rohid7401/MarEnMovimiento/Pruebas/Caja Front.png

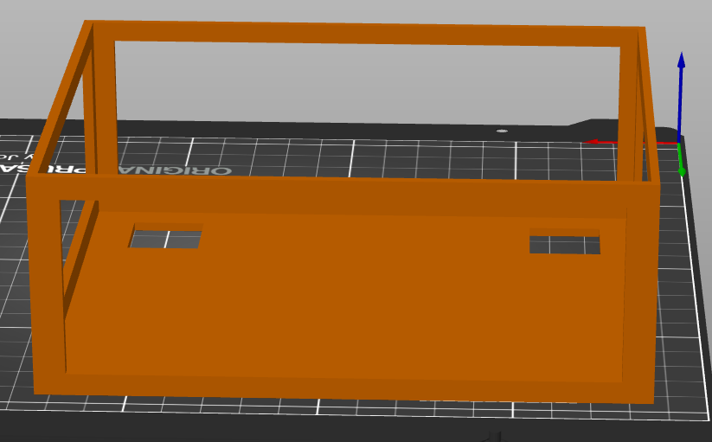
Pruebas/Caja Front.png
