rohid7401/MarEnMovimiento/Pruebas/Caja Top.png

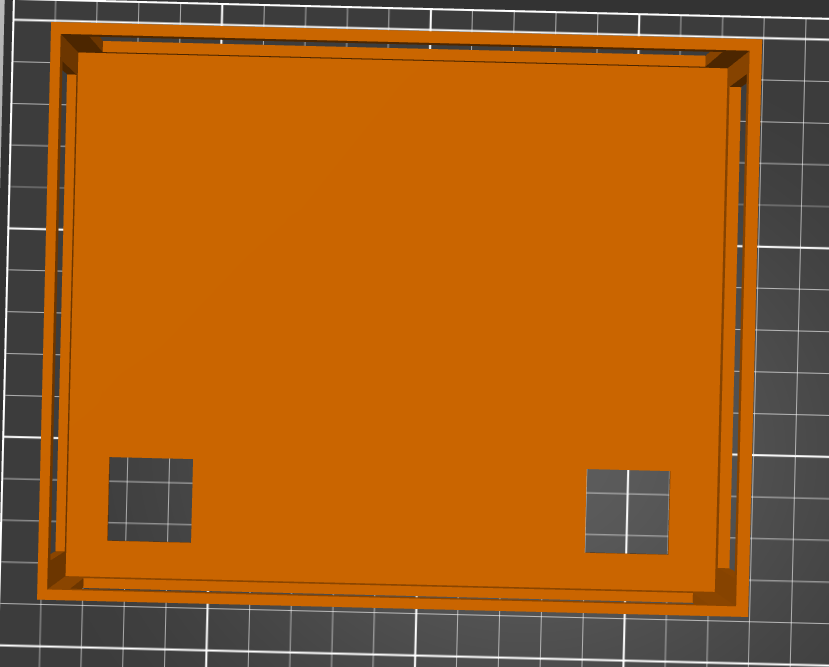
Pruebas/Caja Top.png
