rohid7401/MarEnMovimiento/Pruebas/Engranaje Chico Front.png

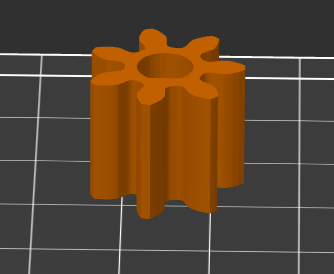
Pruebas/Engranaje Chico Front.png
