rohid7401/MarEnMovimiento/Pruebas/Engranaje Grande Front.png

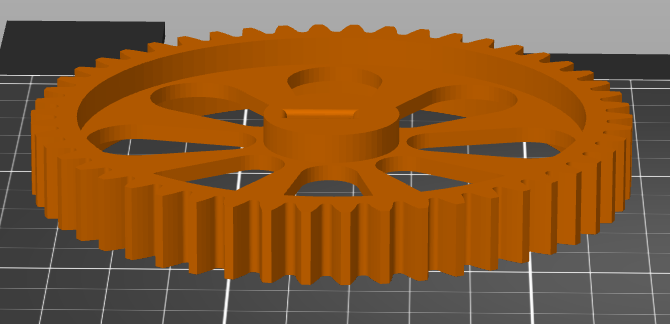
Pruebas/Engranaje Grande Front.png
