rohid7401/MarEnMovimiento/Pruebas/Rosca Top.png

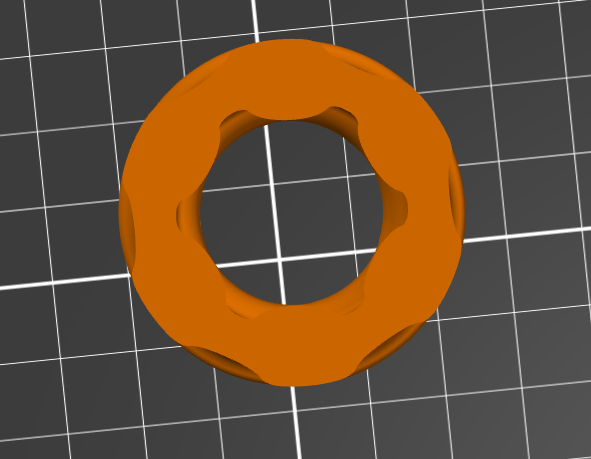
Pruebas/Rosca Top.png
