rohid7401/MarEnMovimiento/Pruebas/Tapa de cilindro Top.png

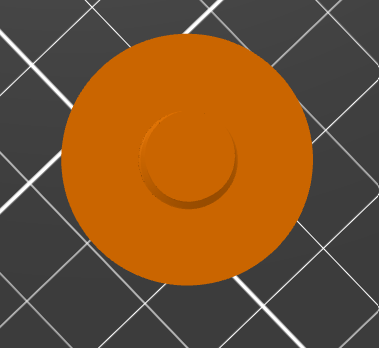
Pruebas/Tapa de cilindro Top.png
